KubiV/TOSULY-Filament-Scale/Hardware/PCB_V01/PDFs/FilamentSpoolScale-B_Mask.pdf

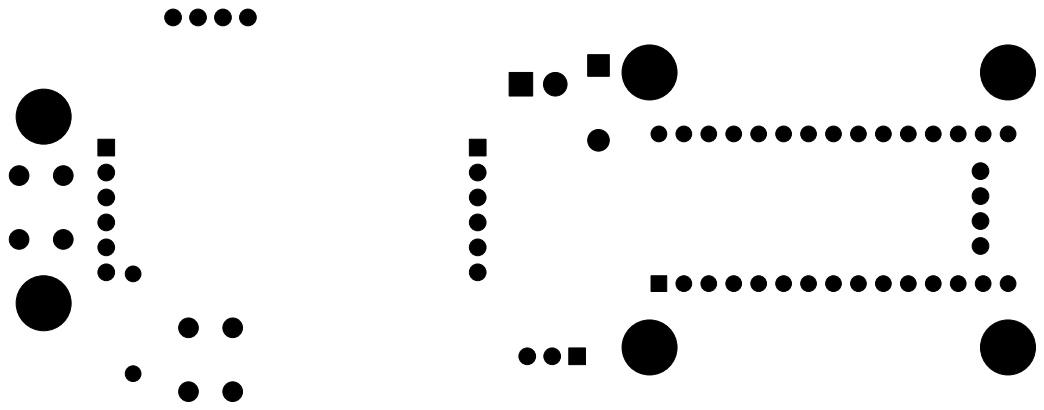
[picture p28: page 1]
