KubiV/TOSULY-Filament-Scale/Hardware/PCB_V01/PDFs/FilamentSpoolScale-B_Silkscreen.pdf

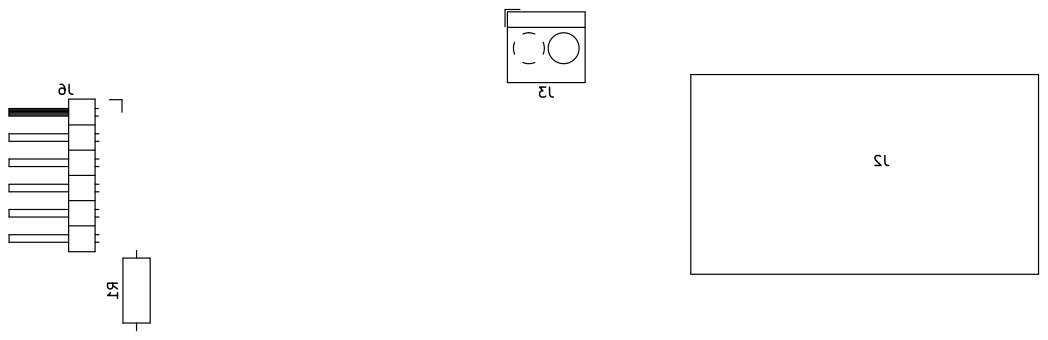
[picture p29: page 1]
