KubiV/TOSULY-Filament-Scale/Hardware/PCB_V01/PDFs/FilamentSpoolScale-Edge_Cuts.pdf

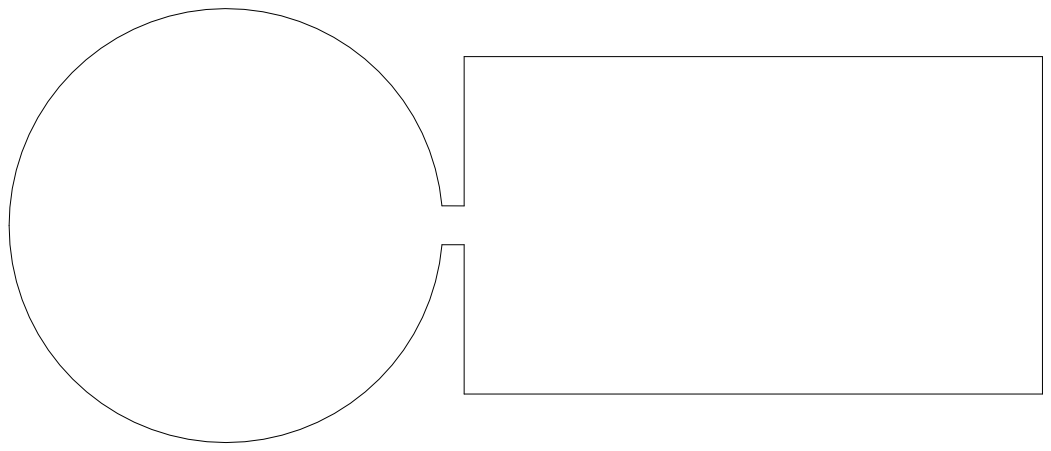
[picture p30: page 1]
