KubiV/TOSULY-Filament-Scale/Hardware/PCB_V01/PDFs/FilamentSpoolScale-F_Cu.pdf

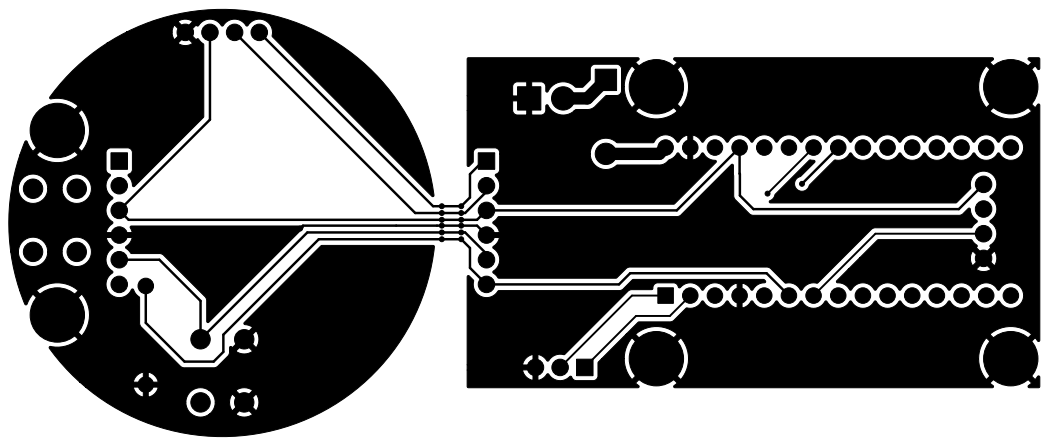
[picture p31: page 1]
