KubiV/TOSULY-Filament-Scale/Hardware/PCB_V01/PDFs/FilamentSpoolScale-F_Silkscreen.pdf

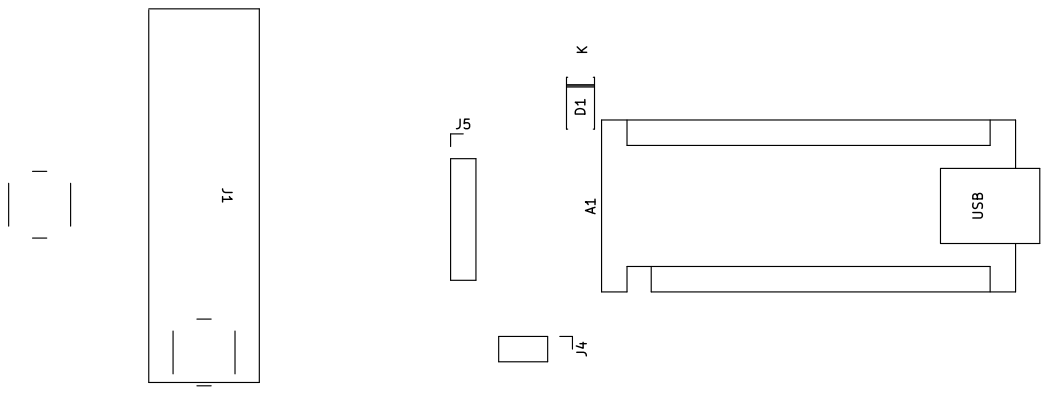
[picture p32: page 1]
